cristianoag/wozblaster/docs/27c160.jpg

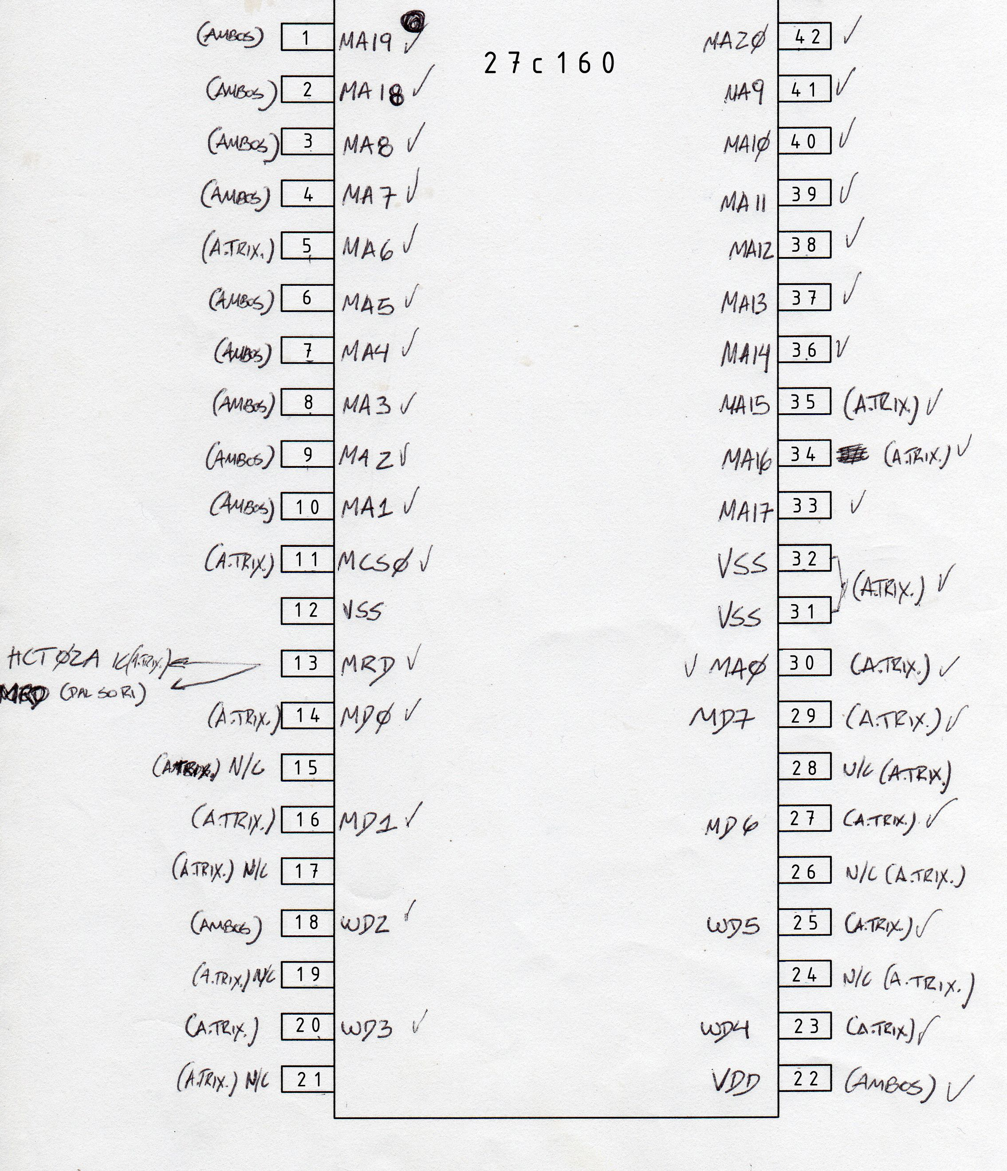
docs/27c160.jpg
