cristianoag/wozblaster/docs/YRW801.jpg

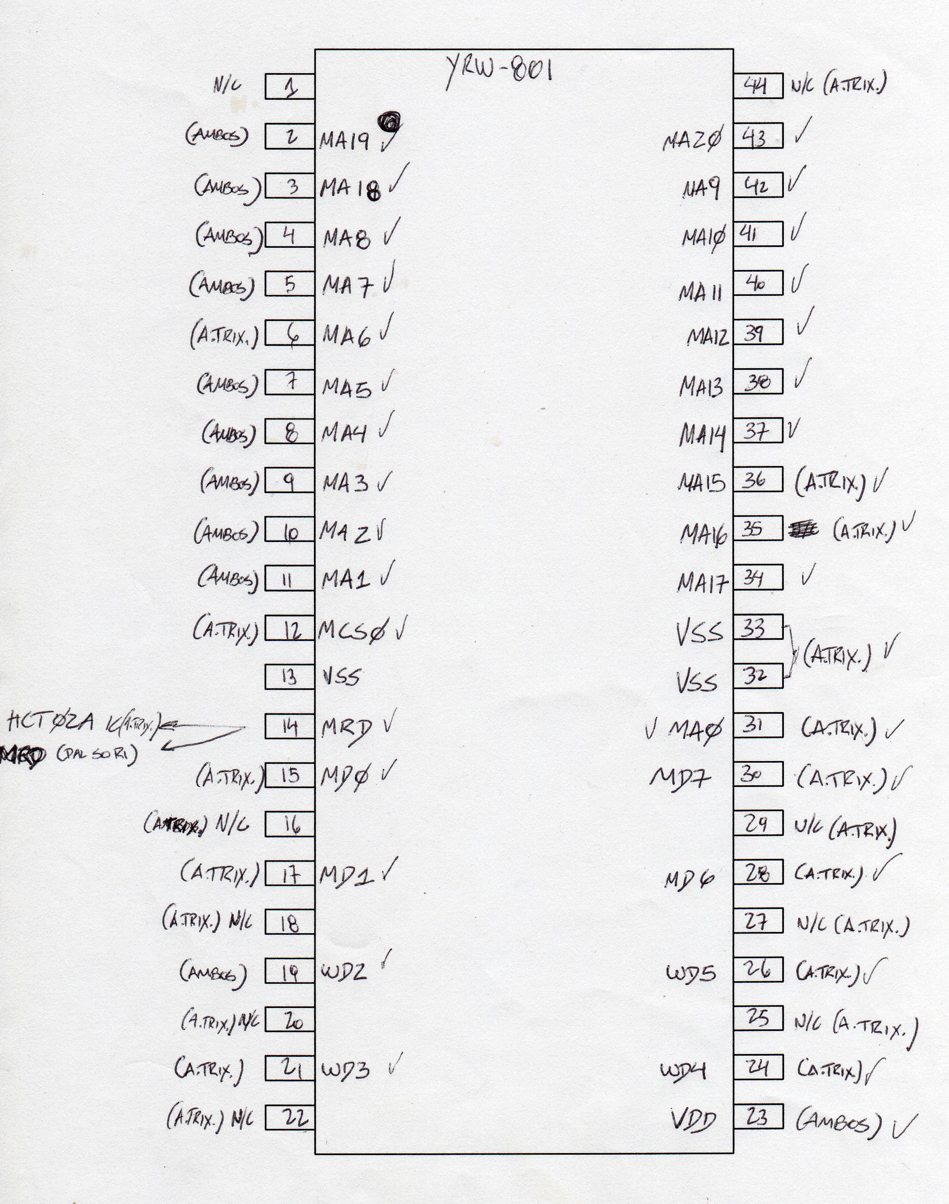
docs/YRW801.jpg
