cristianoag/wozblaster/hardware/rom/Wozblaster - Direcionamiento MSX-OPL.png

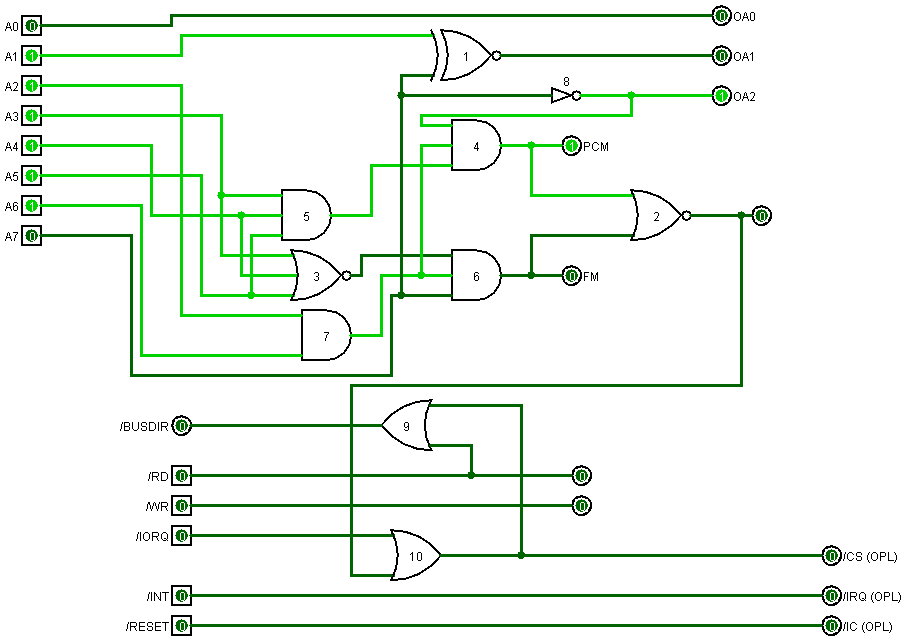
hardware/rom/Wozblaster - Direcionamiento MSX-OPL.png
