cristianoag/wozblaster/hardware/v1/Woazblaster V1.0.png

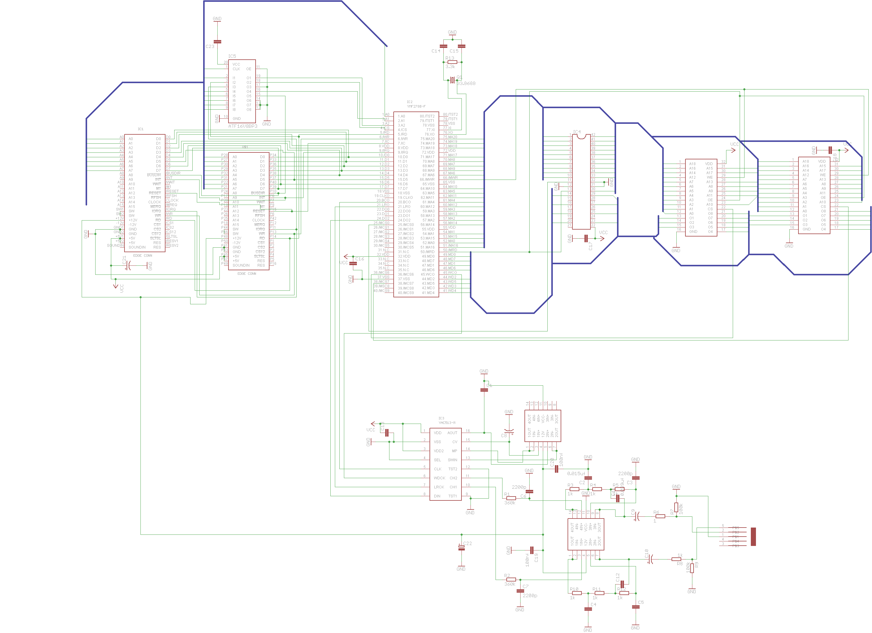
hardware/v1/Woazblaster V1.0.png
