cristianoag/wozblaster/images/2023-03-22_19-14.jpg

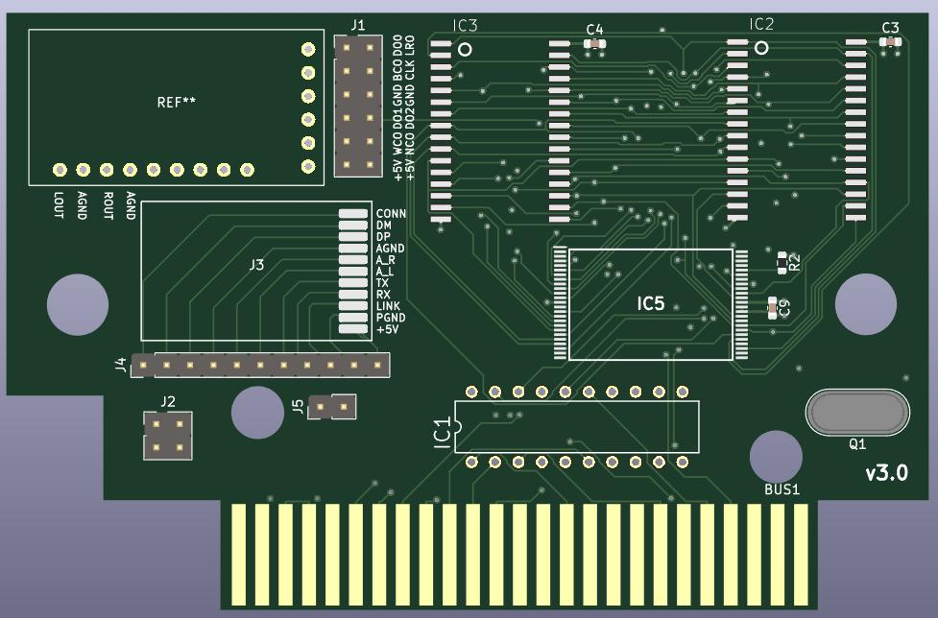
images/2023-03-22_19-14.jpg
