cristianoag/wozblaster/images/2023-08-27_09-25.jpg

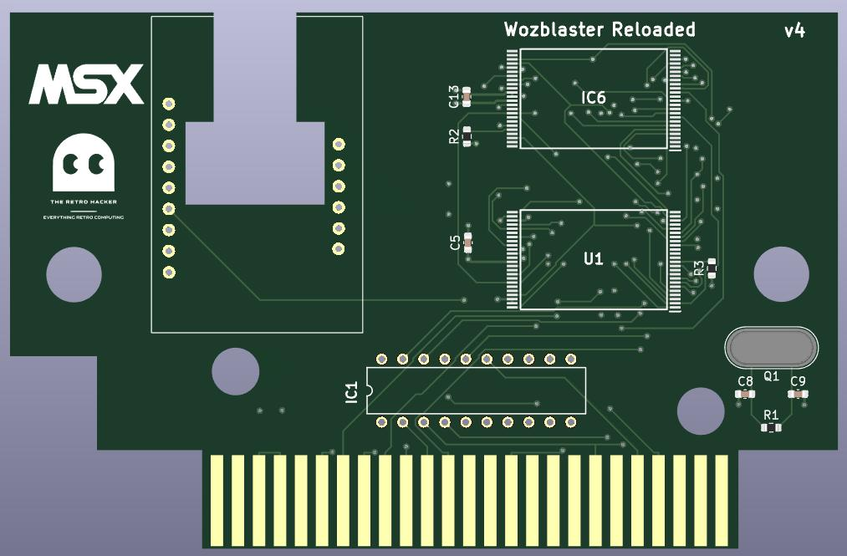
images/2023-08-27_09-25.jpg
