cristianoag/wozblaster/images/20230101_212444857_iOS (Medium).jpg

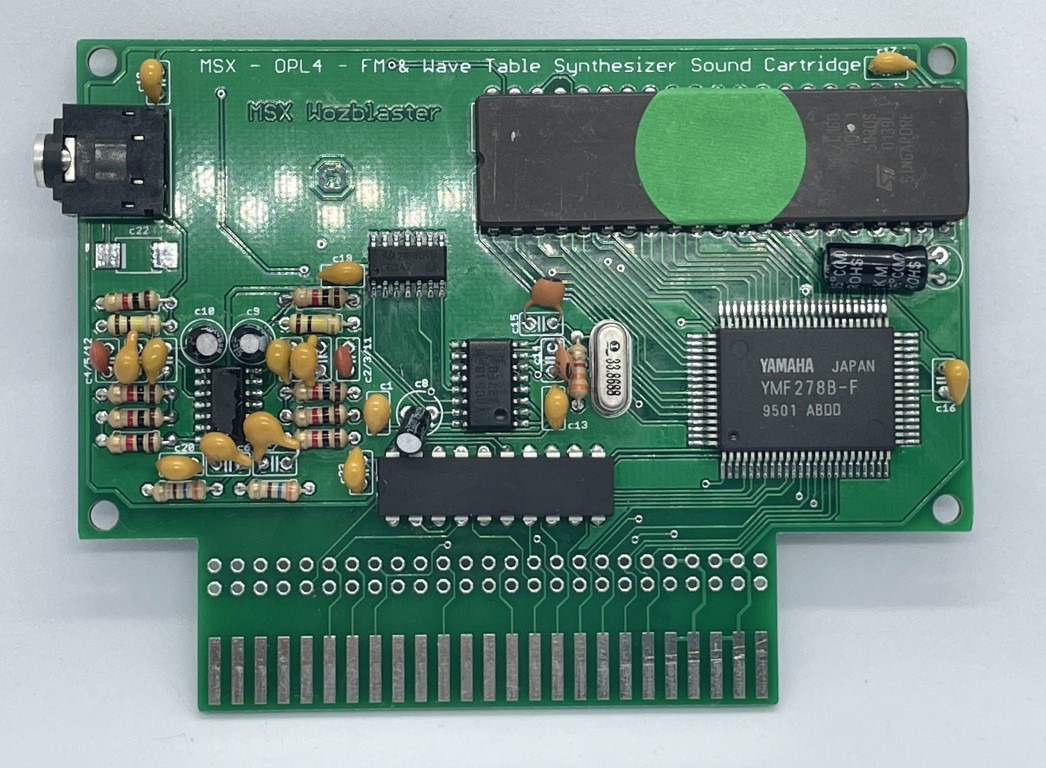
images/20230101_212444857_iOS (Medium).jpg
