cristianoag/wozblaster/images/20230104_165251493_iOS (Medium).jpg

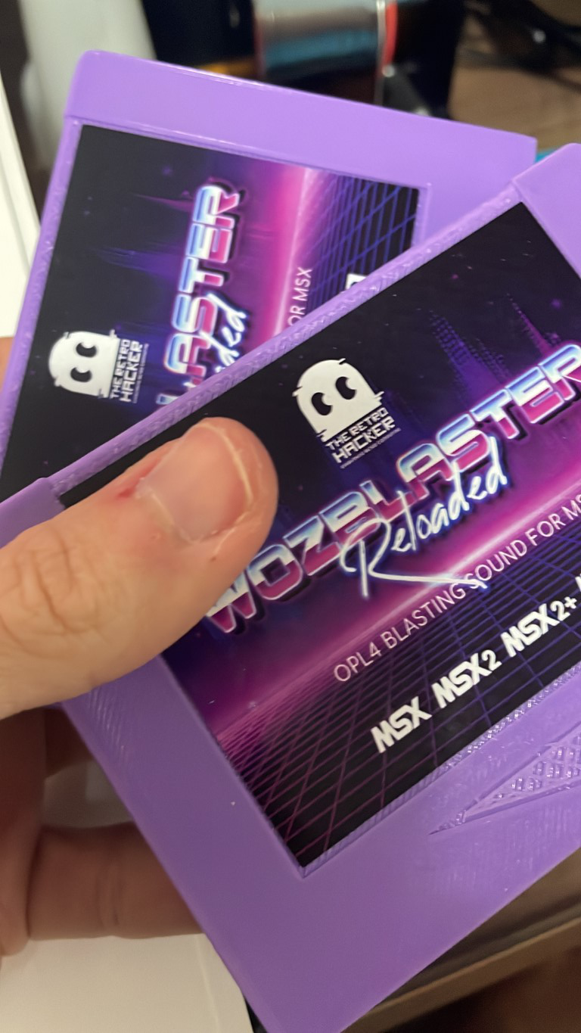
images/20230104_165251493_iOS (Medium).jpg
