cristianoag/wozblaster/images/20230104_171821379_iOS.jpg

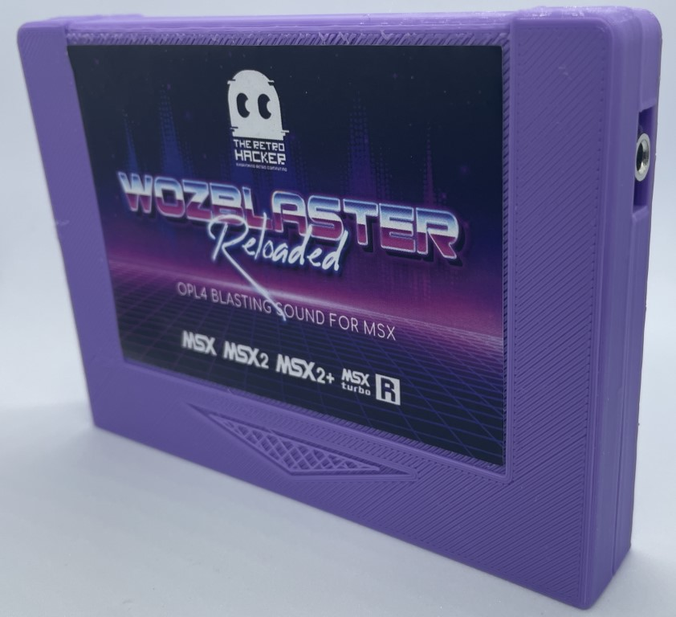
images/20230104_171821379_iOS.jpg
