cristianoag/wozblaster/labels/Wozblaster_Reloaded_Patola_72x51.jpg

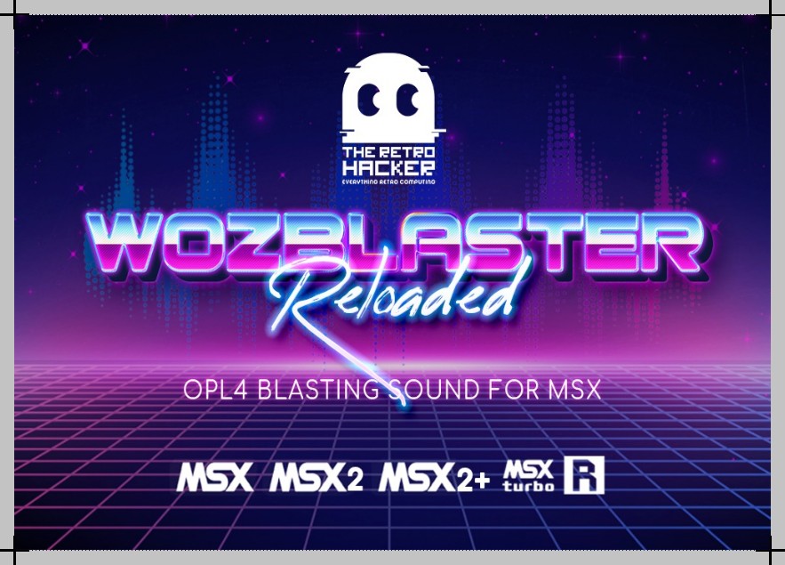
labels/Wozblaster_Reloaded_Patola_72x51.jpg
