cristianoag/wozblaster/labels/Wozblaster_Reloaded_Patola_top_86x12.png

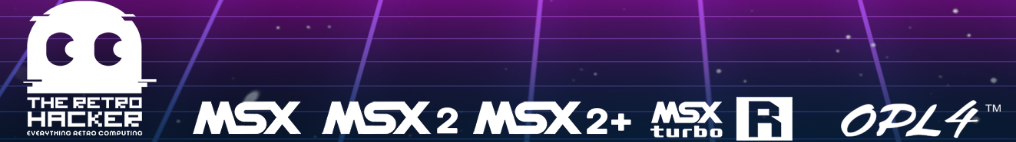
labels/Wozblaster_Reloaded_Patola_top_86x12.png
