cristianoag/wozblaster/hardware/reloaded_v4.5/MSX OPL4 Wozblaster/MSX OPL4 Wozblaster.kicad_sch

## KiCad design hardware/reloaded_v4.5/MSX OPL4 Wozblaster/MSX OPL4 Wozblaster.kicad_sch (2024-11-18)

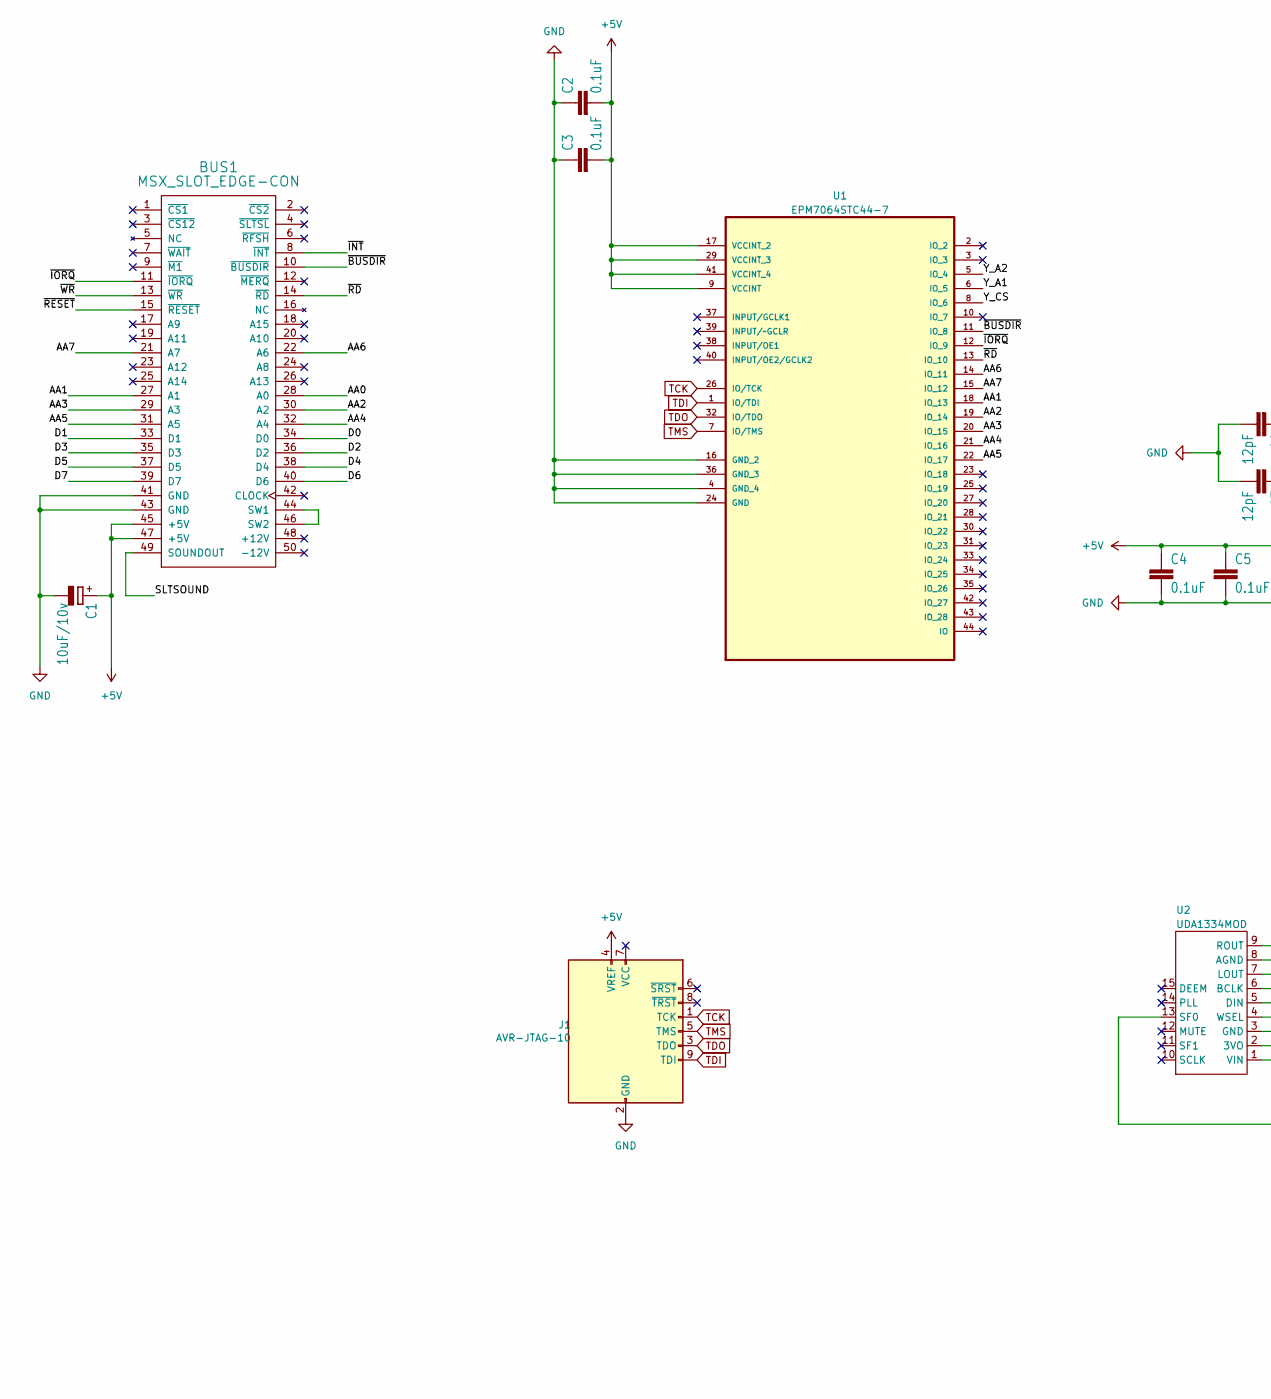
[picture p34: schematic MSX OPL4 Wozblaster.kicad_sch, part in row 1, column 1]

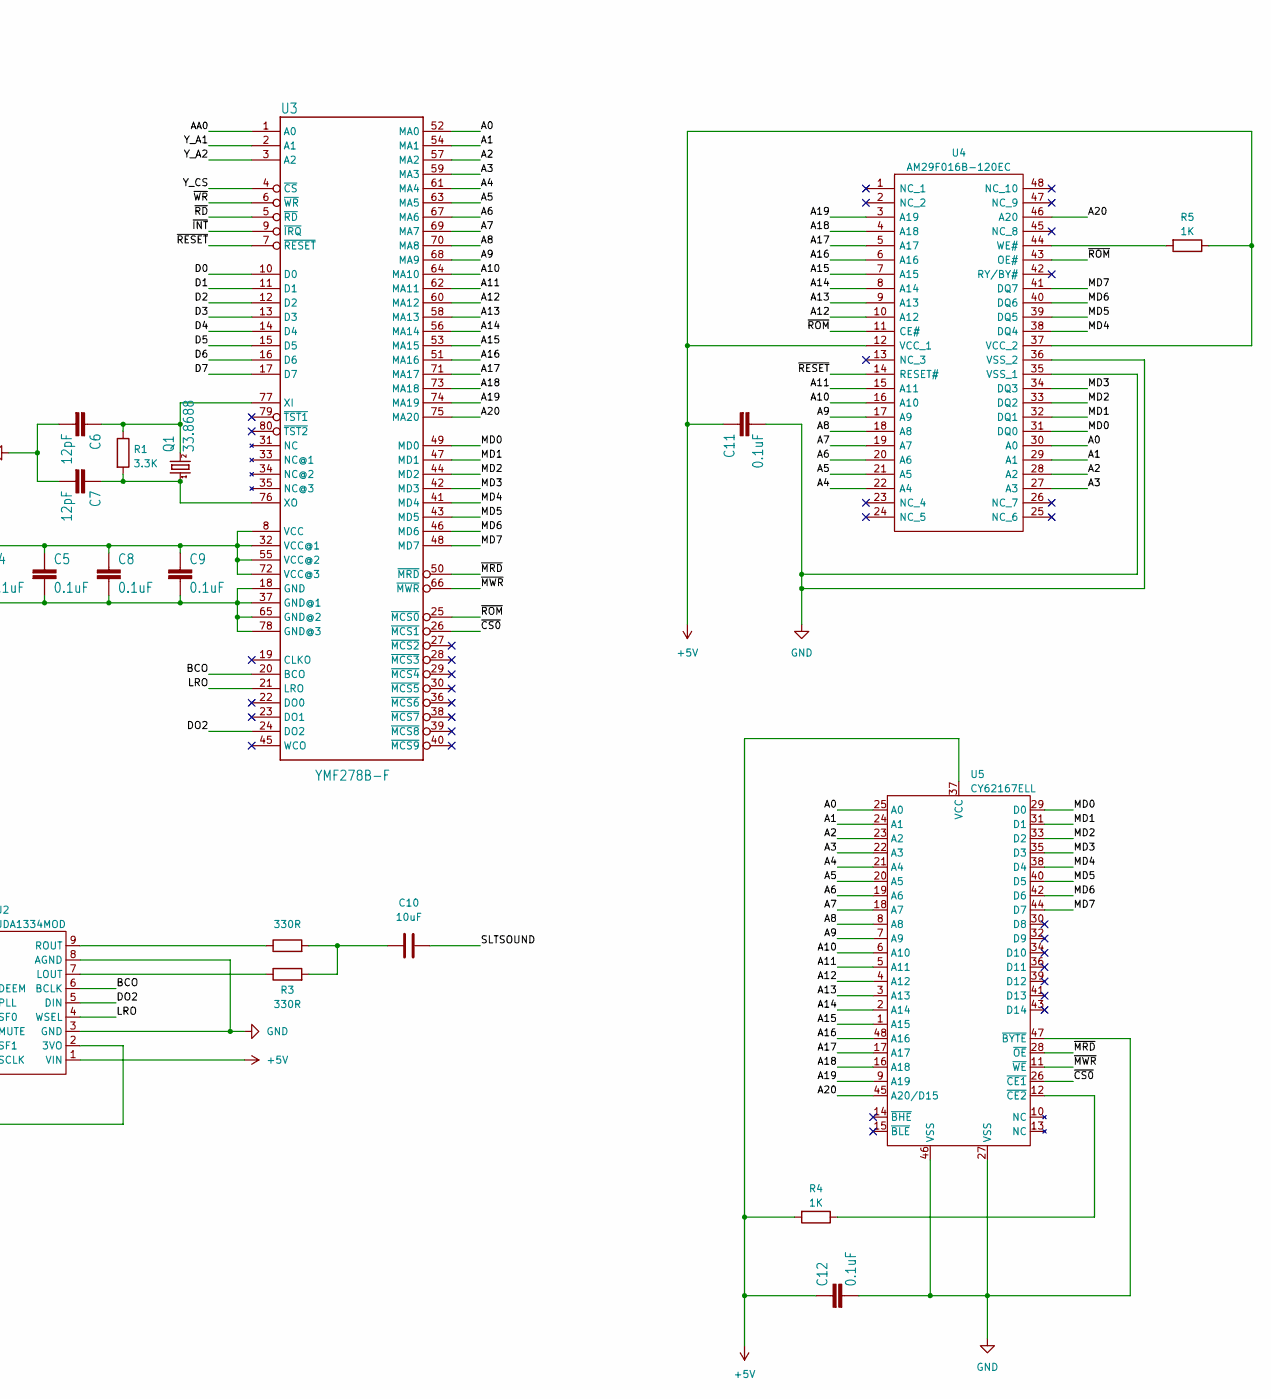
[picture p35: schematic MSX OPL4 Wozblaster.kicad_sch, part in row 1, column 2]

Parts:
BUS1: MSX_SLOT_EDGE-CON; msx_cartridge; MPN n/a
C1: 10uF/10v; CP_EIA-3216-18_Kemet-A
C2, C3, C4, C5, C8, C9, C11, C12: 0.1uF; C_0603_1608Metric
C6, C7: 12pF; C_0603_1608Metric
C10: 10uF; C_0603_1608Metric
J1: AVR-JTAG-10; PinHeader_2x05_P2.54mm_Vertical
Q1: 33.8688; Crystal_HC49-U_Vertical
R1: 3.3K; R_0603_1608Metric
R2, R3: 330R; R_0603_1608Metric
R4, R5: 1K; R_0603_1608Metric
U1: EPM7064STC44-7; QFP80P1200X1200X120-44N; MPN EPM7064STC44-7
U2: UDA1334MOD
U3: YMF278B-F; 80-QFP
U4: AM29F016B-120EC; SOP50P2000X120-48N; Manufacturer_Part_Number AM29F016B-120EC
U5: CY62167ELL; SOP50P2000X120-48N

Connections:
+5V: BUS1.45 (+5V), BUS1.47 (+5V), C1.1 (+), C2.2, C3.2, C4.1, C5.1, C8.1, C9.1, C11.1, C12.1, J1.4 (VREF), R4.2, R5.1, U1.9 (VCCINT), U1.17 (VCCINT_2), U1.29 (VCCINT_3), U1.41 (VCCINT_4), U2.1 (VIN), U3.8 (VCC), U3.32 (VCC@1), U3.55 (VCC@2), U3.72 (VCC@3), U4.12 (VCC_1), U4.37 (VCC_2), U5.37 (VCC)
A0: U3.52 (MA0), U4.30 (A0), U5.25 (A0)
A1: U3.54 (MA1), U4.29 (A1), U5.24 (A1)
A2: U3.57 (MA2), U4.28 (A2), U5.23 (A2)
A3: U3.59 (MA3), U4.27 (A3), U5.22 (A3)
A4: U3.61 (MA4), U4.22 (A4), U5.21 (A4)
A5: U3.63 (MA5), U4.21 (A5), U5.20 (A5)
A6: U3.67 (MA6), U4.20 (A6), U5.19 (A6)
A7: U3.69 (MA7), U4.19 (A7), U5.18 (A7)
A8: U3.70 (MA8), U4.18 (A8), U5.8 (A8)
A9: U3.68 (MA9), U4.17 (A9), U5.7 (A9)
A10: U3.64 (MA10), U4.16 (A10), U5.6 (A10)
A11: U3.62 (MA11), U4.15 (A11), U5.5 (A11)
A12: U3.60 (MA12), U4.10 (A12), U5.4 (A12)
A13: U3.58 (MA13), U4.9 (A13), U5.3 (A13)
A14: U3.56 (MA14), U4.8 (A14), U5.2 (A14)
A15: U3.53 (MA15), U4.7 (A15), U5.1 (A15)
A16: U3.51 (MA16), U4.6 (A16), U5.48 (A16)
A17: U3.71 (MA17), U4.5 (A17), U5.17 (A17)
A18: U3.73 (MA18), U4.4 (A18), U5.16 (A18)
A19: U3.74 (MA19), U4.3 (A19), U5.9 (A19)
A20: U3.75 (MA20), U4.46 (A20), U5.45 (A20/D15)
AA0: BUS1.28 (A0), U3.1 (A0)
AA1: BUS1.27 (A1), U1.18 (IO_13)
AA2: BUS1.30 (A2), U1.19 (IO_14)
AA3: BUS1.29 (A3), U1.20 (IO_15)
AA4: BUS1.32 (A4), U1.21 (IO_16)
AA5: BUS1.31 (A5), U1.22 (IO_17)
AA6: BUS1.22 (A6), U1.14 (IO_11)
AA7: BUS1.21 (A7), U1.15 (IO_12)
BCO: U2.6 (BCLK), U3.20 (BCO)
D0: BUS1.34 (D0), U3.10 (D0)
D1: BUS1.33 (D1), U3.11 (D1)
D2: BUS1.36 (D2~), U3.12 (D2)
D3: BUS1.35 (D3), U3.13 (D3)
D4: BUS1.38 (D4), U3.14 (D4)
D5: BUS1.37 (D5), U3.15 (D5)
D6: BUS1.40 (D6), U3.16 (D6)
D7: BUS1.39 (D7), U3.17 (D7)
DO2: U2.5 (DIN), U3.24 (DO2)
GND: BUS1.41 (GND), BUS1.43 (GND), C1.2 (-), C2.1, C3.1, C4.2, C5.2, C6.2, C7.2, C8.2, C9.2, C11.2, C12.2, J1.2 (GND), J1.10 (GND), U1.4 (GND_4), U1.16 (GND_2), U1.24 (GND), U1.36 (GND_3), U2.3 (GND), U2.8 (AGND), U3.18 (GND), U3.37 (GND@1), U3.65 (GND@2), U3.78 (GND@3), U4.35 (VSS_1), U4.36 (VSS_2), U5.27 (VSS), U5.46 (VSS), U5.47 (~BYTE)
LRO: U2.4 (WSEL), U3.21 (LRO)
MD0: U3.49 (MD0), U4.31 (DQ0), U5.29 (D0)
MD1: U3.47 (MD1), U4.32 (DQ1), U5.31 (D1)
MD2: U3.44 (MD2), U4.33 (DQ2), U5.33 (D2)
MD3: U3.42 (MD3), U4.34 (DQ3), U5.35 (D3)
MD4: U3.41 (MD4), U4.38 (DQ4), U5.38 (D4)
MD5: U3.43 (MD5), U4.39 (DQ5), U5.40 (D5)
MD6: U3.46 (MD6), U4.40 (DQ6), U5.42 (D6)
MD7: U3.48 (MD7), U4.41 (DQ7), U5.44 (D7)
unnamed: BUS1.44 (SW1), BUS1.46 (SW2)
unnamed: C6.1, Q1.2, R1.1, U3.77 (XI)
unnamed: C7.1, Q1.1, R1.2, U3.76 (XO)
unnamed: C10.1, R2.2, R3.2
unnamed: R2.1, U2.9 (ROUT)
unnamed: R3.1, U2.7 (LOUT)
unnamed: R4.1, U5.12 (~CE2)
unnamed: R5.2, U4.44 (WE#)
unnamed: U2.2 (3VO), U2.13 (SF0)
SLTSOUND: BUS1.49 (SOUNDOUT), C10.2
TCK: J1.1 (TCK), U1.26 (IO/TCK)
TDI: J1.9 (TDI), U1.1 (IO/TDI)
TDO: J1.3 (TDO), U1.32 (IO/TDO)
TMS: J1.5 (TMS), U1.7 (IO/TMS)
Y_A1: U1.6 (IO_5), U3.2 (A1)
Y_A2: U1.5 (IO_4), U3.3 (A2)
Y_CS: U1.8 (IO_6), U3.4 (~CS)
~BUSDIR: BUS1.10 (~BUSDIR), U1.11 (IO_8)
~CS0: U3.26 (~MCS1), U5.26 (~CE1)
~INT: BUS1.8 (~INT), U3.9 (~IRQ)
~IORQ: BUS1.11 (~IORQ), U1.12 (IO_9)
~MRD: U3.50 (~MRD), U5.28 (~OE)
~MWR: U3.66 (~MWR), U5.11 (~WE)
~RD: BUS1.14 (~RD), U1.13 (IO_10), U3.5 (~RD)
~RESET: BUS1.15 (~RESET), U3.7 (~RESET), U4.14 (RESET#)
~ROM: U3.25 (~MCS0), U4.11 (CE#), U4.43 (OE#)
~WR: BUS1.13 (~WR), U3.6 (~WR)
